tompi/expensivo/case/expensivo-pcb.scad

// Generated by scripts/gen_case.py from pcb/expensivo.kicad_pcb -- do not edit.
// Case coordinates: mm, origin at the board outline's centre, y up, front view.
// Boxes are [x0, y0, x1, y1]; keys are [x, y, rotation].

pcb_center = [126.396, 92.867];
outline = [[-10.954, 46.851], [-10.695, 46.733], [-10.48, 46.546], [-10.326, 46.307], [-10.246, 46.034], [-10.236, 45.892], [-10.236, 43.562], [-10.234, 43.521], [-10.198, 43.089], [-10.185, 43.008], [-10.083, 42.608], [-10.057, 42.53], [-9.891, 42.152], [-9.852, 42.079], [-9.626, 41.734], [-9.575, 41.668], [-9.296, 41.365], [-9.235, 41.309], [-8.909, 41.055], [-8.84, 41.01], [-8.477, 40.814], [-8.402, 40.781], [-8.011, 40.647], [-7.932, 40.627], [-7.514, 40.557], [-7.453, 40.55], [-7.246, 40.542], [-7.226, 40.542], [8.001, 40.542], [8.283, 40.501], [8.542, 40.383], [8.757, 40.196], [8.911, 39.957], [8.917, 39.943], [9.063, 39.612], [9.102, 39.539], [9.328, 39.194], [9.378, 39.128], [9.658, 38.825], [9.718, 38.769], [10.044, 38.515], [10.113, 38.47], [10.476, 38.274], [10.552, 38.241], [10.942, 38.107], [11.022, 38.087], [11.439, 38.017], [11.501, 38.011], [11.707, 38.002], [11.728, 38.002], [26.763, 38.002], [27.044, 37.961], [27.303, 37.843], [27.518, 37.656], [27.672, 37.417], [27.752, 37.144], [27.763, 37.002], [27.763, 35.637], [27.764, 35.596], [27.8, 35.164], [27.814, 35.083], [27.915, 34.683], [27.942, 34.605], [28.107, 34.227], [28.147, 34.154], [28.372, 33.809], [28.423, 33.743], [28.703, 33.44], [28.763, 33.384], [29.089, 33.13], [29.158, 33.085], [29.521, 32.889], [29.597, 32.856], [29.987, 32.722], [30.067, 32.702], [30.484, 32.632], [30.546, 32.626], [30.752, 32.617], [30.773, 32.617], [48.234, 32.617], [48.516, 32.576], [48.775, 32.458], [48.99, 32.271], [49.144, 32.032], [49.224, 31.759], [49.234, 31.617], [49.234, -23.439], [49.236, -23.48], [49.271, -23.912], [49.285, -23.993], [49.386, -24.393], [49.413, -24.471], [49.579, -24.849], [49.618, -24.922], [49.844, -25.267], [49.895, -25.332], [50.174, -25.636], [50.235, -25.692], [50.56, -25.945], [50.629, -25.99], [51.009, -26.196], [51.049, -26.215], [51.06, -26.22], [51.063, -26.221], [64.875, -32.084], [65.119, -32.232], [65.311, -32.442], [65.436, -32.697], [65.484, -32.978], [65.451, -33.261], [65.405, -33.396], [59.935, -46.283], [59.788, -46.526], [59.578, -46.718], [59.322, -46.843], [59.041, -46.892], [58.759, -46.859], [58.624, -46.812], [44.082, -40.64], [44.043, -40.625], [43.632, -40.489], [43.551, -40.47], [43.144, -40.407], [43.061, -40.401], [42.636, -40.406], [42.591, -40.409], [42.349, -40.397], [25.69, -37.459], [25.609, -37.441], [25.373, -37.379], [25.333, -37.371], [24.906, -37.295], [24.824, -37.288], [24.411, -37.284], [24.329, -37.29], [23.921, -37.354], [23.841, -37.374], [23.441, -37.507], [23.382, -37.531], [23.262, -37.589], [22.991, -37.675], [22.827, -37.688], [6.839, -37.688], [6.557, -37.648], [6.298, -37.53], [6.083, -37.343], [5.929, -37.104], [5.849, -36.831], [5.839, -36.688], [5.839, -22.688], [5.879, -22.407], [5.998, -22.148], [6.184, -21.933], [6.424, -21.779], [6.697, -21.699], [6.839, -21.688], [9.185, -21.688], [9.227, -21.687], [9.658, -21.651], [9.74, -21.637], [10.14, -21.536], [10.218, -21.509], [10.596, -21.344], [10.668, -21.304], [11.014, -21.079], [11.079, -21.028], [11.383, -20.748], [11.439, -20.688], [11.692, -20.362], [11.737, -20.293], [11.934, -19.93], [11.967, -19.854], [12.101, -19.464], [12.121, -19.384], [12.189, -18.977], [12.196, -18.895], [12.196, -18.482], [12.189, -18.4], [12.121, -17.993], [12.101, -17.913], [11.967, -17.522], [11.934, -17.447], [11.737, -17.084], [11.692, -17.015], [11.439, -16.689], [11.383, -16.629], [11.079, -16.349], [11.014, -16.298], [10.847, -16.19], [10.634, -16.002], [10.481, -15.761], [10.425, -15.598], [10.406, -15.523], [10.379, -15.445], [10.213, -15.067], [10.174, -14.994], [9.948, -14.649], [9.898, -14.584], [9.618, -14.28], [9.557, -14.224], [9.232, -13.971], [9.163, -13.926], [8.8, -13.729], [8.724, -13.696], [8.334, -13.562], [8.254, -13.542], [7.837, -13.472], [7.775, -13.466], [7.569, -13.457], [7.548, -13.457], [-7.487, -13.457], [-7.768, -13.416], [-8.027, -13.298], [-8.242, -13.112], [-8.396, -12.872], [-8.476, -12.599], [-8.487, -12.457], [-8.487, -10.128], [-8.488, -10.086], [-8.524, -9.654], [-8.538, -9.573], [-8.639, -9.173], [-8.666, -9.095], [-8.832, -8.717], [-8.871, -8.644], [-9.097, -8.299], [-9.147, -8.234], [-9.427, -7.93], [-9.487, -7.874], [-9.813, -7.621], [-9.882, -7.576], [-10.245, -7.379], [-10.321, -7.346], [-10.711, -7.212], [-10.791, -7.192], [-11.208, -7.122], [-11.27, -7.116], [-11.476, -7.107], [-11.497, -7.107], [-26.214, -7.107], [-26.256, -7.109], [-26.688, -7.144], [-26.769, -7.158], [-27.169, -7.259], [-27.247, -7.286], [-27.625, -7.452], [-27.698, -7.491], [-28.043, -7.717], [-28.108, -7.767], [-28.412, -8.047], [-28.468, -8.108], [-28.721, -8.433], [-28.766, -8.502], [-28.963, -8.865], [-28.996, -8.941], [-29.13, -9.331], [-29.15, -9.411], [-29.22, -9.829], [-29.226, -9.89], [-29.235, -10.097], [-29.235, -10.117], [-29.235, -12.457], [-29.276, -12.739], [-29.394, -12.998], [-29.58, -13.213], [-29.82, -13.366], [-30.093, -13.447], [-30.235, -13.457], [-45.214, -13.457], [-45.255, -13.459], [-45.687, -13.494], [-45.768, -13.508], [-46.168, -13.609], [-46.246, -13.636], [-46.624, -13.802], [-46.697, -13.841], [-47.042, -14.067], [-47.107, -14.117], [-47.411, -14.397], [-47.467, -14.458], [-47.72, -14.783], [-47.765, -14.852], [-47.962, -15.215], [-47.995, -15.291], [-48.129, -15.681], [-48.149, -15.761], [-48.219, -16.179], [-48.225, -16.24], [-48.234, -16.447], [-48.234, -16.467], [-48.234, -22.464], [-48.275, -22.746], [-48.393, -23.005], [-48.579, -23.22], [-48.819, -23.374], [-49.092, -23.454], [-49.234, -23.464], [-64.484, -23.464], [-64.766, -23.424], [-65.025, -23.306], [-65.24, -23.119], [-65.394, -22.88], [-65.474, -22.607], [-65.484, -22.464], [-65.484, -7.712], [-65.444, -7.43], [-65.364, -7.236], [-65.346, -7.203], [-65.313, -7.128], [-65.179, -6.737], [-65.159, -6.657], [-65.091, -6.25], [-65.084, -6.168], [-65.084, -5.755], [-65.091, -5.673], [-65.159, -5.266], [-65.179, -5.186], [-65.316, -4.786], [-65.34, -4.729], [-65.383, -4.642], [-65.47, -4.371], [-65.484, -4.203], [-65.484, 11.288], [-65.444, 11.569], [-65.364, 11.763], [-65.346, 11.796], [-65.313, 11.871], [-65.179, 12.262], [-65.159, 12.342], [-65.091, 12.749], [-65.084, 12.831], [-65.084, 13.244], [-65.091, 13.326], [-65.159, 13.733], [-65.179, 13.813], [-65.316, 14.213], [-65.34, 14.27], [-65.383, 14.357], [-65.47, 14.628], [-65.484, 14.796], [-65.484, 29.534], [-65.444, 29.816], [-65.326, 30.075], [-65.139, 30.29], [-64.9, 30.444], [-64.627, 30.524], [-64.484, 30.534], [-49.506, 30.534], [-49.464, 30.536], [-49.033, 30.571], [-48.951, 30.585], [-48.551, 30.686], [-48.473, 30.713], [-48.095, 30.879], [-48.023, 30.918], [-47.677, 31.144], [-47.612, 31.195], [-47.308, 31.474], [-47.252, 31.535], [-46.999, 31.86], [-46.954, 31.929], [-46.757, 32.292], [-46.724, 32.368], [-46.59, 32.758], [-46.57, 32.838], [-46.5, 33.256], [-46.494, 33.317], [-46.485, 33.524], [-46.485, 33.544], [-46.485, 39.542], [-46.445, 39.823], [-46.326, 40.082], [-46.14, 40.297], [-45.9, 40.451], [-45.627, 40.531], [-45.485, 40.542], [-30.507, 40.542], [-30.465, 40.543], [-30.033, 40.579], [-29.952, 40.593], [-29.552, 40.694], [-29.474, 40.721], [-29.096, 40.886], [-29.023, 40.926], [-28.678, 41.151], [-28.613, 41.202], [-28.309, 41.482], [-28.253, 41.542], [-28.0, 41.868], [-27.955, 41.937], [-27.758, 42.3], [-27.725, 42.376], [-27.591, 42.766], [-27.571, 42.846], [-27.501, 43.263], [-27.495, 43.325], [-27.486, 43.531], [-27.486, 43.552], [-27.486, 45.892], [-27.445, 46.173], [-27.327, 46.432], [-27.141, 46.647], [-26.901, 46.801], [-26.628, 46.881], [-26.486, 46.892], [-11.236, 46.892]];
keys = [[18.613, 30.002, 0.0], [-38.385, 32.542, 0.0], [-38.385, 13.542, 0.0], [-38.385, -5.457, 0.0], [-57.384, 22.534, 0.0], [-57.384, 3.535, 0.0], [-57.384, -15.464, 0.0], [55.214, -36.674, 157.0], [34.893, -30.958, -10.0], [13.939, -29.688, 0.0], [18.613, 11.002, 0.0], [18.613, -7.997, 0.0], [-0.387, 32.542, 0.0], [-0.387, 13.542, 0.0], [-0.387, -5.457, 0.0], [-19.386, 38.892, 0.0], [-19.386, 19.892, 0.0], [-19.386, 0.893, 0.0]];
mounting_holes = [[27.528, 21.239], [9.684, 1.554], [18.384, -18.893], [-48.425, -6.152], [-10.373, 29.462], [-29.583, 23.134], [-48.451, 13.008], [45.816, -23.465]];
tht_pads = [[29.754, -0.183, 31.454, 1.517], [29.754, -2.723, 31.454, -1.023], [37.104, -19.633, 39.104, -17.633], [32.104, -19.633, 34.104, -17.633], [34.604, -19.633, 36.604, -17.633], [29.004, -12.733, 31.004, -9.533], [40.204, -12.733, 42.204, -9.533], [32.104, -5.133, 34.104, -3.133], [37.104, -5.133, 39.104, -3.133], [46.784, -4.583, 47.684, -3.683], [46.784, -1.583, 47.684, -0.683], [46.784, -1.583, 47.684, -0.683], [46.784, -4.583, 47.684, -3.683], [30.534, 30.417, 32.234, 32.117], [30.534, 27.877, 32.234, 29.577], [30.534, 25.337, 32.234, 27.037], [30.534, 22.797, 32.234, 24.497], [30.534, 20.257, 32.234, 21.957], [30.534, 17.717, 32.234, 19.417], [30.534, 15.177, 32.234, 16.877], [30.534, 12.637, 32.234, 14.337], [30.534, 10.097, 32.234, 11.797], [30.534, 7.557, 32.234, 9.257], [30.534, 5.017, 32.234, 6.717], [30.534, 2.477, 32.234, 4.177], [43.234, 7.557, 44.934, 9.257], [40.694, 7.557, 42.394, 9.257], [38.154, 7.557, 39.854, 9.257], [45.774, 30.417, 47.474, 32.117], [45.774, 27.877, 47.474, 29.577], [45.774, 25.337, 47.474, 27.037], [45.774, 22.797, 47.474, 24.497], [45.774, 20.257, 47.474, 21.957], [45.774, 17.717, 47.474, 19.417], [45.774, 15.177, 47.474, 16.877], [45.774, 12.637, 47.474, 14.337], [45.774, 10.097, 47.474, 11.797], [45.774, 7.557, 47.474, 9.257], [45.774, 5.017, 47.474, 6.717], [45.774, 2.477, 47.474, 4.177]];
pads_front = [[27.528, 21.239, 2.2, 2.2, 0.0, 1, 2.2], [9.684, 1.554, 2.2, 2.2, 0.0, 1, 2.2], [-62.464, 22.534, 1.702, 1.702, 0.0, 1, 1.702], [-59.924, 27.614, 3.0, 3.0, 0.0, 1, 3.0], [-59.924, 17.454, 3.0, 3.0, 0.0, 1, 3.0], [-57.384, 22.534, 3.988, 3.988, 0.0, 1, 3.988], [-53.574, 25.074, 3.0, 3.0, 0.0, 1, 3.0], [-53.574, 19.994, 3.0, 3.0, 0.0, 1, 3.0], [-52.304, 22.534, 1.702, 1.702, 0.0, 1, 1.702], [-63.674, 27.614, 2.55, 2.5, 0.0, 0, 0], [-61.194, 25.074, 2.286, 2.286, 0.0, 1, 1.499], [-61.194, 19.994, 2.286, 2.286, 0.0, 1, 1.499], [-54.844, 27.614, 2.286, 2.286, 0.0, 1, 1.499], [-54.844, 17.454, 2.286, 2.286, 0.0, 1, 1.499], [-49.824, 25.074, 2.55, 2.5, 0.0, 0, 0], [13.533, -7.997, 1.702, 1.702, 0.0, 1, 1.702], [16.073, -2.917, 3.0, 3.0, 0.0, 1, 3.0], [16.073, -13.077, 3.0, 3.0, 0.0, 1, 3.0], [18.613, -7.997, 3.988, 3.988, 0.0, 1, 3.988], [22.423, -5.457, 3.0, 3.0, 0.0, 1, 3.0], [22.423, -10.537, 3.0, 3.0, 0.0, 1, 3.0], [23.693, -7.997, 1.702, 1.702, 0.0, 1, 1.702], [12.323, -2.917, 2.55, 2.5, 0.0, 0, 0], [14.803, -5.457, 2.286, 2.286, 0.0, 1, 1.499], [14.803, -10.537, 2.286, 2.286, 0.0, 1, 1.499], [21.153, -2.917, 2.286, 2.286, 0.0, 1, 1.499], [21.153, -13.077, 2.286, 2.286, 0.0, 1, 1.499], [26.173, -5.457, 2.55, 2.5, 0.0, 0, 0], [13.533, 30.002, 1.702, 1.702, 0.0, 1, 1.702], [16.073, 35.082, 3.0, 3.0, 0.0, 1, 3.0], [16.073, 24.922, 3.0, 3.0, 0.0, 1, 3.0], [18.613, 30.002, 3.988, 3.988, 0.0, 1, 3.988], [22.423, 32.542, 3.0, 3.0, 0.0, 1, 3.0], [22.423, 27.462, 3.0, 3.0, 0.0, 1, 3.0], [23.693, 30.002, 1.702, 1.702, 0.0, 1, 1.702], [12.323, 35.082, 2.55, 2.5, 0.0, 0, 0], [14.803, 32.542, 2.286, 2.286, 0.0, 1, 1.499], [14.803, 27.462, 2.286, 2.286, 0.0, 1, 1.499], [21.153, 35.082, 2.286, 2.286, 0.0, 1, 1.499], [21.153, 24.922, 2.286, 2.286, 0.0, 1, 1.499], [26.173, 32.542, 2.55, 2.5, 0.0, 0, 0], [-24.466, 19.892, 1.702, 1.702, 0.0, 1, 1.702], [-21.926, 24.972, 3.0, 3.0, 0.0, 1, 3.0], [-21.926, 14.812, 3.0, 3.0, 0.0, 1, 3.0], [-19.386, 19.892, 3.988, 3.988, 0.0, 1, 3.988], [-15.576, 22.432, 3.0, 3.0, 0.0, 1, 3.0], [-15.576, 17.352, 3.0, 3.0, 0.0, 1, 3.0], [-14.306, 19.892, 1.702, 1.702, 0.0, 1, 1.702], [-25.676, 24.972, 2.55, 2.5, 0.0, 0, 0], [-23.196, 22.432, 2.286, 2.286, 0.0, 1, 1.499], [-23.196, 17.352, 2.286, 2.286, 0.0, 1, 1.499], [-16.846, 24.972, 2.286, 2.286, 0.0, 1, 1.499], [-16.846, 14.812, 2.286, 2.286, 0.0, 1, 1.499], [-11.826, 22.432, 2.55, 2.5, 0.0, 0, 0], [18.384, -18.893, 2.2, 2.2, 0.0, 1, 2.2], [-43.465, -5.457, 1.702, 1.702, 0.0, 1, 1.702], [-40.925, -0.377, 3.0, 3.0, 0.0, 1, 3.0], [-40.925, -10.537, 3.0, 3.0, 0.0, 1, 3.0], [-38.385, -5.457, 3.988, 3.988, 0.0, 1, 3.988], [-34.575, -2.917, 3.0, 3.0, 0.0, 1, 3.0], [-34.575, -7.997, 3.0, 3.0, 0.0, 1, 3.0], [-33.305, -5.457, 1.702, 1.702, 0.0, 1, 1.702], [-44.675, -0.377, 2.55, 2.5, 0.0, 0, 0], [-42.195, -2.917, 2.286, 2.286, 0.0, 1, 1.499], [-42.195, -7.997, 2.286, 2.286, 0.0, 1, 1.499], [-35.845, -0.377, 2.286, 2.286, 0.0, 1, 1.499], [-35.845, -10.537, 2.286, 2.286, 0.0, 1, 1.499], [-30.825, -2.917, 2.55, 2.5, 0.0, 0, 0], [44.004, -16.283, 1.7, 1.0, 90.0, 0, 0], [44.004, -9.983, 1.7, 1.0, 90.0, 0, 0], [47.804, -16.283, 1.7, 1.0, 90.0, 0, 0], [47.804, -9.983, 1.7, 1.0, 90.0, 0, 0], [31.384, 31.267, 1.7, 1.7, 0.0, 0, 1.0], [31.384, 28.727, 1.7, 1.7, 0.0, 1, 1.0], [31.384, 26.187, 1.7, 1.7, 0.0, 1, 1.0], [31.384, 23.647, 1.7, 1.7, 0.0, 1, 1.0], [31.384, 21.107, 1.7, 1.7, 0.0, 1, 1.0], [31.384, 18.567, 1.7, 1.7, 0.0, 1, 1.0], [31.384, 16.027, 1.7, 1.7, 0.0, 1, 1.0], [31.384, 13.487, 1.7, 1.7, 0.0, 1, 1.0], [31.384, 10.947, 1.7, 1.7, 0.0, 1, 1.0], [31.384, 8.407, 1.7, 1.7, 0.0, 1, 1.0], [31.384, 5.867, 1.7, 1.7, 0.0, 1, 1.0], [31.384, 3.327, 1.7, 1.7, 0.0, 1, 1.0], [44.084, 8.407, 1.7, 1.7, 0.0, 1, 1.0], [41.544, 8.407, 1.7, 1.7, 0.0, 1, 1.0], [39.004, 8.407, 1.7, 1.7, 0.0, 1, 1.0], [46.624, 31.267, 1.7, 1.7, 0.0, 1, 1.0], [46.624, 28.727, 1.7, 1.7, 0.0, 1, 1.0], [46.624, 26.187, 1.7, 1.7, 0.0, 1, 1.0], [46.624, 23.647, 1.7, 1.7, 0.0, 1, 1.0], [46.624, 21.107, 1.7, 1.7, 0.0, 1, 1.0], [46.624, 18.567, 1.7, 1.7, 0.0, 1, 1.0], [46.624, 16.027, 1.7, 1.7, 0.0, 1, 1.0], [46.624, 13.487, 1.7, 1.7, 0.0, 1, 1.0], [46.624, 10.947, 1.7, 1.7, 0.0, 1, 1.0], [46.624, 8.407, 1.7, 1.7, 0.0, 1, 1.0], [46.624, 5.867, 1.7, 1.7, 0.0, 1, 1.0], [46.624, 3.327, 1.7, 1.7, 0.0, 1, 1.0], [-48.425, -6.152, 2.2, 2.2, 0.0, 1, 2.2], [33.659, 31.267, 0.3, 0.3, 0.0, 0, 0], [35.109, 31.267, 0.3, 0.3, 0.0, 0, 0], [-43.465, 13.542, 1.702, 1.702, 0.0, 1, 1.702], [-40.925, 18.622, 3.0, 3.0, 0.0, 1, 3.0], [-40.925, 8.462, 3.0, 3.0, 0.0, 1, 3.0], [-38.385, 13.542, 3.988, 3.988, 0.0, 1, 3.988], [-34.575, 16.082, 3.0, 3.0, 0.0, 1, 3.0], [-34.575, 11.002, 3.0, 3.0, 0.0, 1, 3.0], [-33.305, 13.542, 1.702, 1.702, 0.0, 1, 1.702], [-44.675, 18.622, 2.55, 2.5, 0.0, 0, 0], [-42.195, 16.082, 2.286, 2.286, 0.0, 1, 1.499], [-42.195, 11.002, 2.286, 2.286, 0.0, 1, 1.499], [-35.845, 18.622, 2.286, 2.286, 0.0, 1, 1.499], [-35.845, 8.462, 2.286, 2.286, 0.0, 1, 1.499], [-30.825, 16.082, 2.55, 2.5, 0.0, 0, 0], [33.659, 28.727, 0.3, 0.3, 0.0, 0, 0], [35.109, 28.727, 0.3, 0.3, 0.0, 0, 0], [30.604, 0.667, 1.7, 1.7, 0.0, 0, 1.0], [30.604, -1.873, 1.7, 1.7, 0.0, 1, 1.0], [-62.464, 3.535, 1.702, 1.702, 0.0, 1, 1.702], [-59.924, 8.615, 3.0, 3.0, 0.0, 1, 3.0], [-59.924, -1.545, 3.0, 3.0, 0.0, 1, 3.0], [-57.384, 3.535, 3.988, 3.988, 0.0, 1, 3.988], [-53.574, 6.075, 3.0, 3.0, 0.0, 1, 3.0], [-53.574, 0.995, 3.0, 3.0, 0.0, 1, 3.0], [-52.304, 3.535, 1.702, 1.702, 0.0, 1, 1.702], [-63.674, 8.615, 2.55, 2.5, 0.0, 0, 0], [-61.194, 6.075, 2.286, 2.286, 0.0, 1, 1.499], [-61.194, 0.995, 2.286, 2.286, 0.0, 1, 1.499], [-54.844, 8.615, 2.286, 2.286, 0.0, 1, 1.499], [-54.844, -1.545, 2.286, 2.286, 0.0, 1, 1.499], [-49.824, 6.075, 2.55, 2.5, 0.0, 0, 0], [-10.373, 29.462, 2.2, 2.2, 0.0, 1, 2.2], [44.349, 31.267, 0.3, 0.3, 180.0, 0, 0], [42.899, 31.267, 0.3, 0.3, 180.0, 0, 0], [-5.467, 13.542, 1.702, 1.702, 0.0, 1, 1.702], [-2.927, 18.622, 3.0, 3.0, 0.0, 1, 3.0], [-2.927, 8.462, 3.0, 3.0, 0.0, 1, 3.0], [-0.387, 13.542, 3.988, 3.988, 0.0, 1, 3.988], [3.423, 16.082, 3.0, 3.0, 0.0, 1, 3.0], [3.423, 11.002, 3.0, 3.0, 0.0, 1, 3.0], [4.693, 13.542, 1.702, 1.702, 0.0, 1, 1.702], [-6.677, 18.622, 2.55, 2.5, 0.0, 0, 0], [-4.197, 16.082, 2.286, 2.286, 0.0, 1, 1.499], [-4.197, 11.002, 2.286, 2.286, 0.0, 1, 1.499], [2.153, 18.622, 2.286, 2.286, 0.0, 1, 1.499], [2.153, 8.462, 2.286, 2.286, 0.0, 1, 1.499], [7.173, 16.082, 2.55, 2.5, 0.0, 0, 0], [-5.467, 32.542, 1.702, 1.702, 0.0, 1, 1.702], [-2.927, 37.622, 3.0, 3.0, 0.0, 1, 3.0], [-2.927, 27.462, 3.0, 3.0, 0.0, 1, 3.0], [-0.387, 32.542, 3.988, 3.988, 0.0, 1, 3.988], [3.423, 35.082, 3.0, 3.0, 0.0, 1, 3.0], [3.423, 30.002, 3.0, 3.0, 0.0, 1, 3.0], [4.693, 32.542, 1.702, 1.702, 0.0, 1, 1.702], [-6.677, 37.622, 2.55, 2.5, 0.0, 0, 0], [-4.197, 35.082, 2.286, 2.286, 0.0, 1, 1.499], [-4.197, 30.002, 2.286, 2.286, 0.0, 1, 1.499], [2.153, 37.622, 2.286, 2.286, 0.0, 1, 1.499], [2.153, 27.462, 2.286, 2.286, 0.0, 1, 1.499], [7.173, 35.082, 2.55, 2.5, 0.0, 0, 0], [-62.464, -15.464, 1.702, 1.702, 0.0, 1, 1.702], [-59.924, -10.384, 3.0, 3.0, 0.0, 1, 3.0], [-59.924, -20.544, 3.0, 3.0, 0.0, 1, 3.0], [-57.384, -15.464, 3.988, 3.988, 0.0, 1, 3.988], [-53.574, -12.924, 3.0, 3.0, 0.0, 1, 3.0], [-53.574, -18.004, 3.0, 3.0, 0.0, 1, 3.0], [-52.304, -15.464, 1.702, 1.702, 0.0, 1, 1.702], [-63.674, -10.384, 2.55, 2.5, 0.0, 0, 0], [-61.194, -12.924, 2.286, 2.286, 0.0, 1, 1.499], [-61.194, -18.004, 2.286, 2.286, 0.0, 1, 1.499], [-54.844, -10.384, 2.286, 2.286, 0.0, 1, 1.499], [-54.844, -20.544, 2.286, 2.286, 0.0, 1, 1.499], [-49.824, -12.924, 2.55, 2.5, 0.0, 0, 0], [46.124, -6.283, 1.0, 0.8, 90.0, 0, 0], [48.334, -6.283, 1.0, 0.8, 90.0, 0, 0], [47.234, -4.133, 0.9, 0.9, 90.0, 1, 0.9], [47.234, -1.133, 0.9, 0.9, 90.0, 1, 0.9], [46.124, 1.017, 1.0, 0.8, 90.0, 0, 0], [48.334, 1.017, 1.0, 0.8, 90.0, 0, 0], [45.474, -4.883, 0.7, 1.5, 90.0, 0, 0], [45.474, -1.883, 0.7, 1.5, 90.0, 0, 0], [45.474, -0.383, 0.7, 1.5, 90.0, 0, 0], [29.89, -30.076, 1.702, 1.702, 350.0, 1, 1.702], [33.274, -25.515, 3.0, 3.0, 350.0, 1, 3.0], [31.509, -35.52, 3.0, 3.0, 350.0, 1, 3.0], [34.893, -30.958, 3.988, 3.988, 350.0, 1, 3.988], [39.086, -29.119, 3.0, 3.0, 350.0, 1, 3.0], [38.204, -34.121, 3.0, 3.0, 350.0, 1, 3.0], [39.896, -31.841, 1.702, 1.702, 350.0, 1, 1.702], [29.581, -24.863, 2.55, 2.5, 350.0, 0, 0], [31.582, -27.795, 2.286, 2.286, 350.0, 1, 1.499], [30.7, -32.798, 2.286, 2.286, 350.0, 1, 1.499], [38.276, -26.397, 2.286, 2.286, 350.0, 1, 1.499], [36.512, -36.402, 2.286, 2.286, 350.0, 1, 1.499], [42.779, -29.77, 2.55, 2.5, 350.0, 0, 0], [-29.583, 23.134, 2.2, 2.2, 0.0, 1, 2.2], [8.859, -29.688, 1.702, 1.702, 0.0, 1, 1.702], [11.399, -24.608, 3.0, 3.0, 0.0, 1, 3.0], [11.399, -34.768, 3.0, 3.0, 0.0, 1, 3.0], [13.939, -29.688, 3.988, 3.988, 0.0, 1, 3.988], [17.749, -27.148, 3.0, 3.0, 0.0, 1, 3.0], [17.749, -32.228, 3.0, 3.0, 0.0, 1, 3.0], [19.019, -29.688, 1.702, 1.702, 0.0, 1, 1.702], [7.649, -24.608, 2.55, 2.5, 0.0, 0, 0], [10.129, -27.148, 2.286, 2.286, 0.0, 1, 1.499], [10.129, -32.228, 2.286, 2.286, 0.0, 1, 1.499], [16.479, -24.608, 2.286, 2.286, 0.0, 1, 1.499], [16.479, -34.768, 2.286, 2.286, 0.0, 1, 1.499], [21.499, -27.148, 2.55, 2.5, 0.0, 0, 0], [-48.451, 13.008, 2.2, 2.2, 0.0, 1, 2.2], [-43.465, 32.542, 1.702, 1.702, 0.0, 1, 1.702], [-40.925, 37.622, 3.0, 3.0, 0.0, 1, 3.0], [-40.925, 27.462, 3.0, 3.0, 0.0, 1, 3.0], [-38.385, 32.542, 3.988, 3.988, 0.0, 1, 3.988], [-34.575, 35.082, 3.0, 3.0, 0.0, 1, 3.0], [-34.575, 30.002, 3.0, 3.0, 0.0, 1, 3.0], [-33.305, 32.542, 1.702, 1.702, 0.0, 1, 1.702], [-44.675, 37.622, 2.55, 2.5, 0.0, 0, 0], [-42.195, 35.082, 2.286, 2.286, 0.0, 1, 1.499], [-42.195, 30.002, 2.286, 2.286, 0.0, 1, 1.499], [-35.845, 37.622, 2.286, 2.286, 0.0, 1, 1.499], [-35.845, 27.462, 2.286, 2.286, 0.0, 1, 1.499], [-30.825, 35.082, 2.55, 2.5, 0.0, 0, 0], [13.533, 11.002, 1.702, 1.702, 0.0, 1, 1.702], [16.073, 16.082, 3.0, 3.0, 0.0, 1, 3.0], [16.073, 5.922, 3.0, 3.0, 0.0, 1, 3.0], [18.613, 11.002, 3.988, 3.988, 0.0, 1, 3.988], [22.423, 13.542, 3.0, 3.0, 0.0, 1, 3.0], [22.423, 8.462, 3.0, 3.0, 0.0, 1, 3.0], [23.693, 11.002, 1.702, 1.702, 0.0, 1, 1.702], [12.323, 16.082, 2.55, 2.5, 0.0, 0, 0], [14.803, 13.542, 2.286, 2.286, 0.0, 1, 1.499], [14.803, 8.462, 2.286, 2.286, 0.0, 1, 1.499], [21.153, 16.082, 2.286, 2.286, 0.0, 1, 1.499], [21.153, 5.922, 2.286, 2.286, 0.0, 1, 1.499], [26.173, 13.542, 2.55, 2.5, 0.0, 0, 0], [-24.466, 38.892, 1.702, 1.702, 0.0, 1, 1.702], [-21.926, 43.972, 3.0, 3.0, 0.0, 1, 3.0], [-21.926, 33.812, 3.0, 3.0, 0.0, 1, 3.0], [-19.386, 38.892, 3.988, 3.988, 0.0, 1, 3.988], [-15.576, 41.432, 3.0, 3.0, 0.0, 1, 3.0], [-15.576, 36.352, 3.0, 3.0, 0.0, 1, 3.0], [-14.306, 38.892, 1.702, 1.702, 0.0, 1, 1.702], [-25.676, 43.972, 2.55, 2.5, 0.0, 0, 0], [-23.196, 41.432, 2.286, 2.286, 0.0, 1, 1.499], [-23.196, 36.352, 2.286, 2.286, 0.0, 1, 1.499], [-16.846, 43.972, 2.286, 2.286, 0.0, 1, 1.499], [-16.846, 33.812, 2.286, 2.286, 0.0, 1, 1.499], [-11.826, 41.432, 2.55, 2.5, 0.0, 0, 0], [33.659, 23.647, 0.3, 0.3, 0.0, 0, 0], [35.109, 23.647, 0.3, 0.3, 0.0, 0, 0], [45.816, -23.465, 2.2, 2.2, 0.0, 1, 2.2], [59.89, -38.659, 1.702, 1.702, 157.0, 1, 1.702], [55.567, -42.343, 3.0, 3.0, 157.0, 1, 3.0], [59.537, -32.99, 3.0, 3.0, 157.0, 1, 3.0], [55.214, -36.674, 3.988, 3.988, 157.0, 1, 3.988], [50.714, -37.524, 3.0, 3.0, 157.0, 1, 3.0], [52.699, -32.847, 3.0, 3.0, 157.0, 1, 3.0], [50.538, -34.689, 1.702, 1.702, 157.0, 1, 1.702], [59.019, -43.808, 2.55, 2.5, 157.0, 0, 0], [57.729, -40.501, 2.286, 2.286, 157.0, 1, 1.499], [59.714, -35.825, 2.286, 2.286, 157.0, 1, 1.499], [50.891, -40.358, 2.286, 2.286, 157.0, 1, 1.499], [54.861, -31.006, 2.286, 2.286, 157.0, 1, 1.499], [47.262, -36.058, 2.55, 2.5, 157.0, 0, 0], [-24.466, 0.893, 1.702, 1.702, 0.0, 1, 1.702], [-21.926, 5.973, 3.0, 3.0, 0.0, 1, 3.0], [-21.926, -4.187, 3.0, 3.0, 0.0, 1, 3.0], [-19.386, 0.893, 3.988, 3.988, 0.0, 1, 3.988], [-15.576, 3.433, 3.0, 3.0, 0.0, 1, 3.0], [-15.576, -1.647, 3.0, 3.0, 0.0, 1, 3.0], [-14.306, 0.893, 1.702, 1.702, 0.0, 1, 1.702], [-25.676, 5.973, 2.55, 2.5, 0.0, 0, 0], [-23.196, 3.433, 2.286, 2.286, 0.0, 1, 1.499], [-23.196, -1.647, 2.286, 2.286, 0.0, 1, 1.499], [-16.846, 5.973, 2.286, 2.286, 0.0, 1, 1.499], [-16.846, -4.187, 2.286, 2.286, 0.0, 1, 1.499], [-11.826, 3.433, 2.55, 2.5, 0.0, 0, 0], [-5.467, -5.457, 1.702, 1.702, 0.0, 1, 1.702], [-2.927, -0.377, 3.0, 3.0, 0.0, 1, 3.0], [-2.927, -10.537, 3.0, 3.0, 0.0, 1, 3.0], [-0.387, -5.457, 3.988, 3.988, 0.0, 1, 3.988], [3.423, -2.917, 3.0, 3.0, 0.0, 1, 3.0], [3.423, -7.997, 3.0, 3.0, 0.0, 1, 3.0], [4.693, -5.457, 1.702, 1.702, 0.0, 1, 1.702], [-6.677, -0.377, 2.55, 2.5, 0.0, 0, 0], [-4.197, -2.917, 2.286, 2.286, 0.0, 1, 1.499], [-4.197, -7.997, 2.286, 2.286, 0.0, 1, 1.499], [2.153, -0.377, 2.286, 2.286, 0.0, 1, 1.499], [2.153, -10.537, 2.286, 2.286, 0.0, 1, 1.499], [7.173, -2.917, 2.55, 2.5, 0.0, 0, 0], [47.234, -1.133, 0.9, 0.9, 270.0, 1, 0.9], [47.234, -4.133, 0.9, 0.9, 270.0, 1, 0.9], [38.104, -18.633, 2.0, 2.0, 90.0, 0, 1.0], [33.104, -18.633, 2.0, 2.0, 90.0, 1, 1.0], [35.604, -18.633, 2.0, 2.0, 90.0, 1, 1.0], [30.004, -11.133, 3.2, 2.0, 90.0, 0, 2.8], [41.204, -11.133, 3.2, 2.0, 90.0, 0, 2.8], [33.104, -4.133, 2.0, 2.0, 90.0, 1, 1.0], [38.104, -4.133, 2.0, 2.0, 90.0, 1, 1.0]];
nano = [30.064, 1.947, 47.944, 35.127];
battery_pads = [29.754, -2.723, 31.454, 1.517];
encoder_body = [29.744, -17.193, 41.464, -5.073];
encoder_pads = [29.004, -19.633, 42.204, -3.133];
power_switch = [44.724, -6.783, 48.734, 1.517];
reset_button = [43.504, -17.133, 48.304, -9.133];
mcu_edge_x = 49.234;
